JelmerT/esp32weatherstation/Firmware/src/storePrefs.ino

/*
 * Note: preference names can't be longer than 15 characters
 */
void loadNetworkCredentials() {
  pref.begin("weather", false);
  ssid = pref.getString("ssid");
  pass = pref.getString("pass");
  pref.end();
}

void storeNetworkCredentials() {
  pref.begin("weather", false);
  pref.putString("ssid", ssid);
  pref.putString("pass", pass);
  pref.end();
}

void loadUploadSettings() {
  pref.begin("weather", false);
  thingspeakEnabled = pref.getBool("thingspeakEn");
  thingspeakApi = pref.getString("thingspeakApi");
  tsfWindSpeed = pref.getInt("tsfWindSpeed");
  tsfWindDir = pref.getInt("tsfWindDir");
  tsfRainAmount = pref.getInt("tsfRainAmount");
  tsfTemperature = pref.getInt("tsfTemperature");
  tsfHumidity = pref.getInt("tsfHumidity");
  tsfAirpressure = pref.getInt("tsfAirpressure");
  tsfPM1 = pref.getInt("tsfPM1");
  tsfPM2 = pref.getInt("tsfPM2");
  tsfPM10 = pref.getInt("tsfPM10");

  senseBoxEnabled = pref.getBool("sbEnabled");
  senseBoxStationId = pref.getString("sbStationId");
  senseBoxTempId = pref.getString("sbTempId");
  senseBoxHumId = pref.getString("sbHumId");
  senseBoxPressId = pref.getString("sbPressId");
  senseBoxWindSId = pref.getString("sbWindSId");
  senseBoxWindDId = pref.getString("sbWindDId");
  senseBoxRainId = pref.getString("sbRainId");
  senseBoxPM1Id = pref.getString("sbPM1Id");
  senseBoxPM2Id = pref.getString("sbPM2Id");
  senseBoxPM10Id = pref.getString("sbPM10Id");
  
  uploadInterval = ((pref.getUInt("uploadInterval") != 0) ? pref.getUInt("uploadInterval") : hourMs);
  pref.end();
}

void storeUploadSettings() {
  pref.begin("weather", false);
  pref.putBool("thingspeakEn", thingspeakEnabled);
  pref.putString("thingspeakApi", thingspeakApi);
  pref.putInt("tsfWindSpeed", tsfWindSpeed);
  pref.putInt("tsfWindDir", tsfWindDir);
  pref.putInt("tsfRainAmount", tsfRainAmount);
  pref.putInt("tsfTemperature", tsfTemperature);
  pref.putInt("tsfHumidity", tsfHumidity);
  pref.putInt("tsfAirpressure", tsfAirpressure);
  pref.putInt("tsfPM1", tsfPM1);
  pref.putInt("tsfPM2", tsfPM2);
  pref.putInt("tsfPM10", tsfPM10);

  pref.putBool("sbEnabled", senseBoxEnabled);
  pref.putString("sbStationId", senseBoxStationId);
  pref.putString("sbTempId", senseBoxTempId);
  pref.putString("sbHumId", senseBoxHumId);
  pref.putString("sbPressId", senseBoxPressId);
  pref.putString("sbWindSId", senseBoxWindSId);
  pref.putString("sbWindDId", senseBoxWindDId);
  pref.putString("sbRainId", senseBoxRainId);
  pref.putString("sbPM1Id", senseBoxPM1Id);
  pref.putString("sbPM2Id", senseBoxPM2Id);
  pref.putString("sbPM10Id", senseBoxPM10Id);
  
  pref.putUInt("uploadInterval", uploadInterval);
  pref.end();
}
